kemerelab/ConstantCurrent/LaserDriverTest/Simulation/LaserDriverSource.asc

C1: Cap; 10µF
C2: Cap; 10µF
R1: Res; 0.33
R2: Res; 20k
R3: Res; 1
U1: LT3083
V1: voltage; 10
Named nets: 0
.tran 1
