kemerelab/ConstantCurrent/OpAmpStimulator/Simulation/OpAmpCurrentSource.asc

C1: Cap; 10µ
R1: Res; 100k
R2: Res; 100k
R3: Res; 5k
R4: Res; 100k
R5: Res; 100k
R6: res; 10k
R7: Res; 10000000
U1: LT6020
U2: LT6020
V1: voltage; 12
V2: voltage; -12
V3: voltage; PULSE(0 1 100u 10n 10n 100u 1m 1)
V4: voltage; PULSE(0 1 220u 10n 10n 100u 1m 1)
Named nets: 0, V+, V-, VOUT, VP1, VP2
.tran 10m
https://www.allaboutcircuits.com/technical-articles/how-to-design-a-precision-current-pump-with-op-amps/
IOUT = VIN * AV / R3
AV = R4/R2, R2=R3, R4=R5
- Consider using https://www.analog.com/en/products/lt6023.html for 10x reduced power and slightly reduced slew rate.
